20lives/dmote/config/dmote/no_bottom.yaml

# Configuration fragment for an open case.
# Key aliases used herein refer to dmote/base.yaml.

case:
  bottom-plate:
    include: false
  foot-plates:
    include: true
    height: 3
    polygons:
    - points:
      - anchor: rear-housing
        corner: NNW
        offset: [0, 0]
      - anchor: rear-housing
        corner: NNW
        offset: [10, 0]
      - anchor: rear-housing
        corner: NNW
        offset: [0, -10]
    - points:
      - anchor: a1
        corner: WNW
        offset: [7, 0]
      - anchor: a1
        corner: NNE
      - anchor: a1
        corner: ESE
        offset: [0, -6]
    - points:
      - anchor: near-right
        corner: SSW
        offset: [4, 1]
      - anchor: near-right
        corner: NNE
        offset: [1, -5]
      - anchor: near-right
        corner: ESE
wrist-rest:
  bottom-plate:
    include: false
